JEEBIS27/Mejiro31/docs/imgs/keyboard_cross.jpg

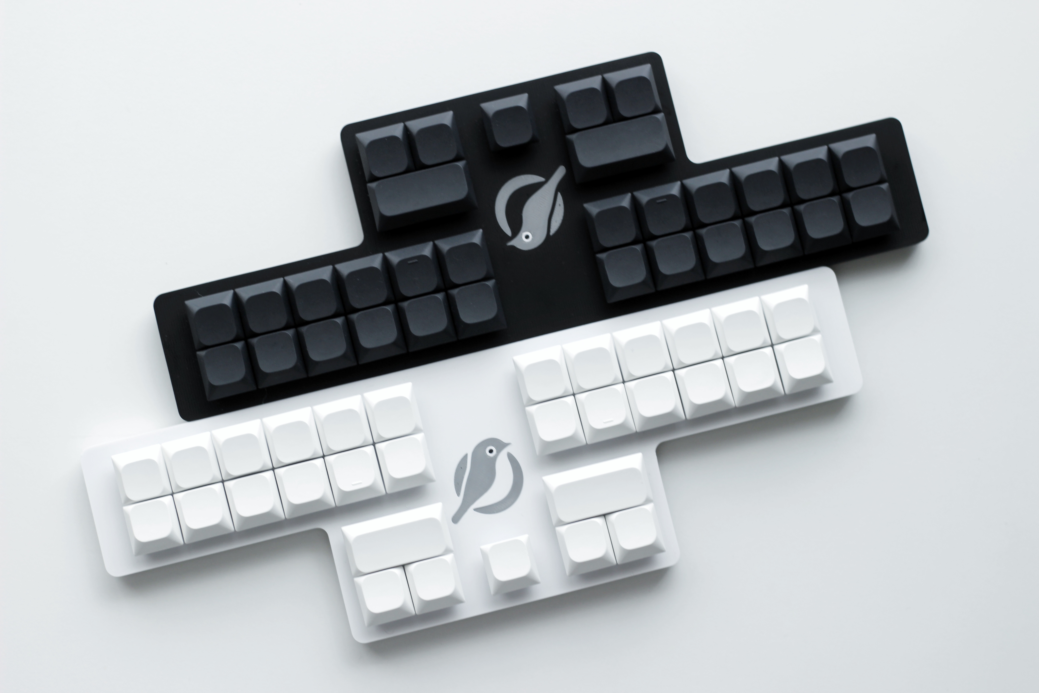
docs/imgs/keyboard_cross.jpg
