JEEBIS27/Mejiro31/docs/imgs/keyboard_front.jpg

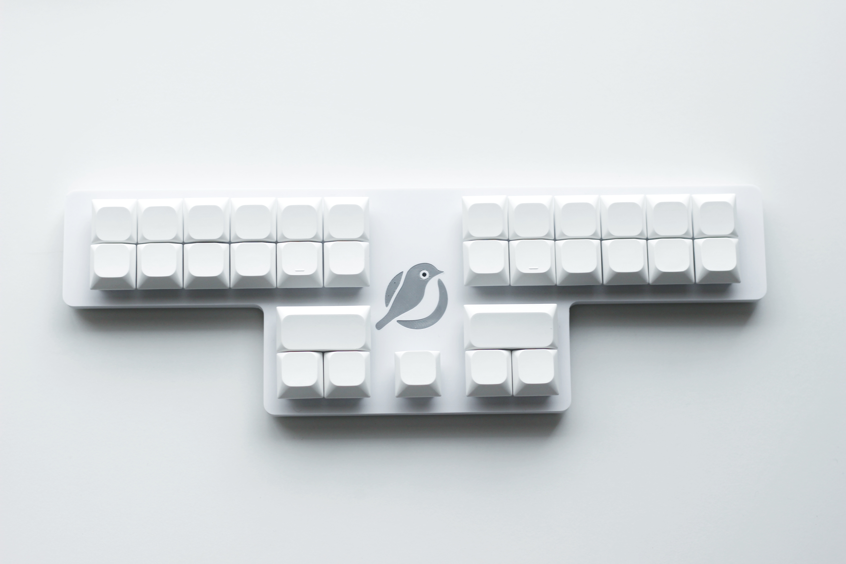
docs/imgs/keyboard_front.jpg
