JEEBIS27/Mejiro31/docs/imgs/win_ime_setting_1.png

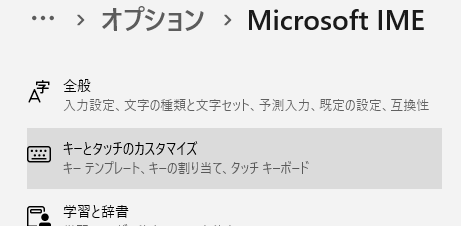
docs/imgs/win_ime_setting_1.png
