JEEBIS27/Mejiro31/docs/imgs/win_ime_setting_2.png

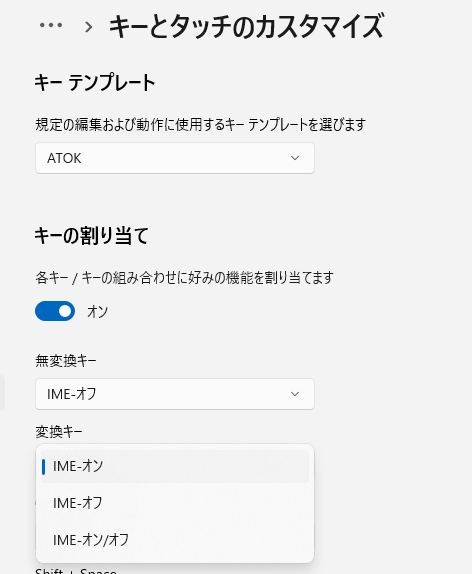
docs/imgs/win_ime_setting_2.png
