JEEBIS27/Mejiro31/docs/imgs/build_sidewall.jpeg

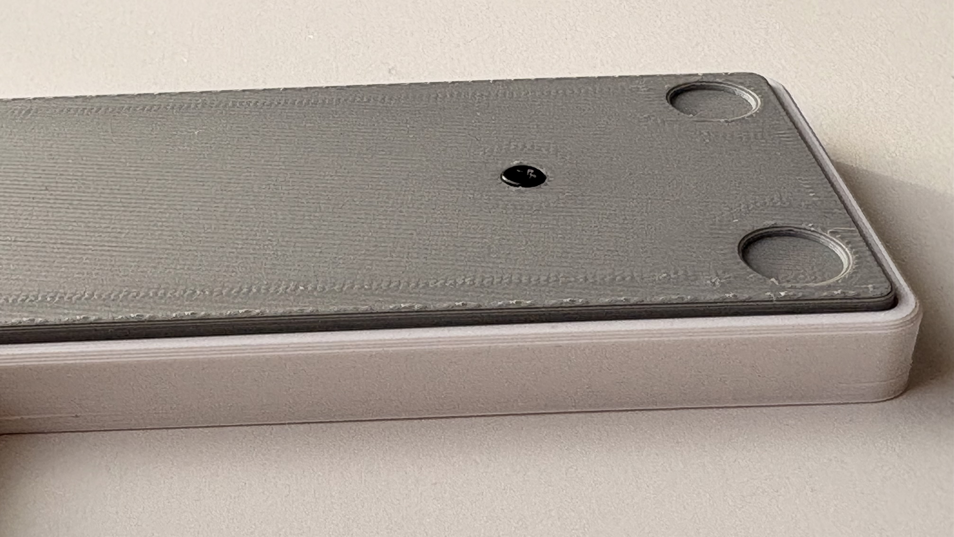
docs/imgs/build_sidewall.jpeg
