JEEBIS27/Mejiro31/docs/imgs/build_trimming_bottom_middle.jpg

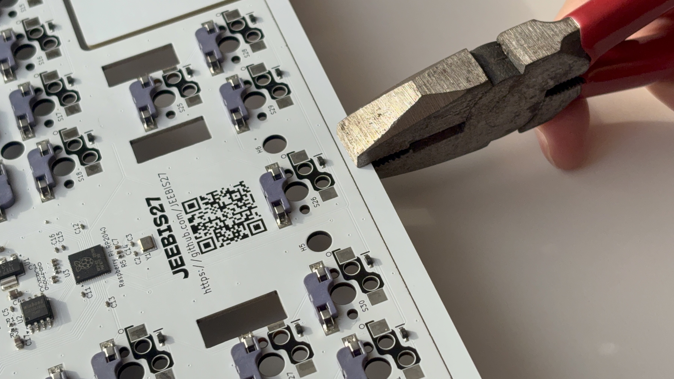
docs/imgs/build_trimming_bottom_middle.jpg
